richardhawthorn/Wifi7Segment-smd/images/DSC_4980.JPG

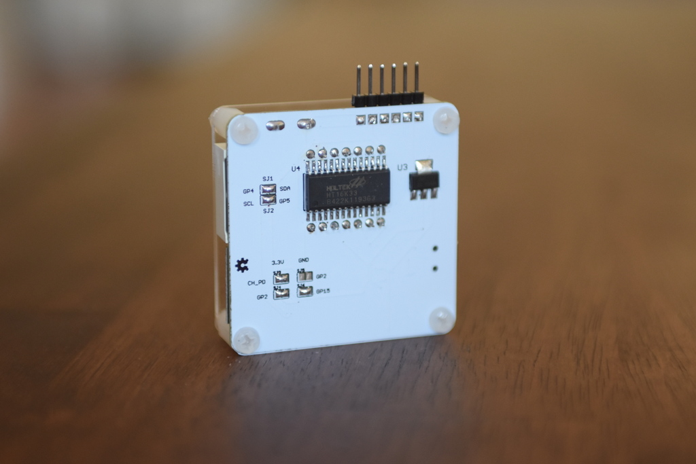
images/DSC_4980.JPG
