richardhawthorn/Wifi7Segment-smd/images/DSC_4983.JPG

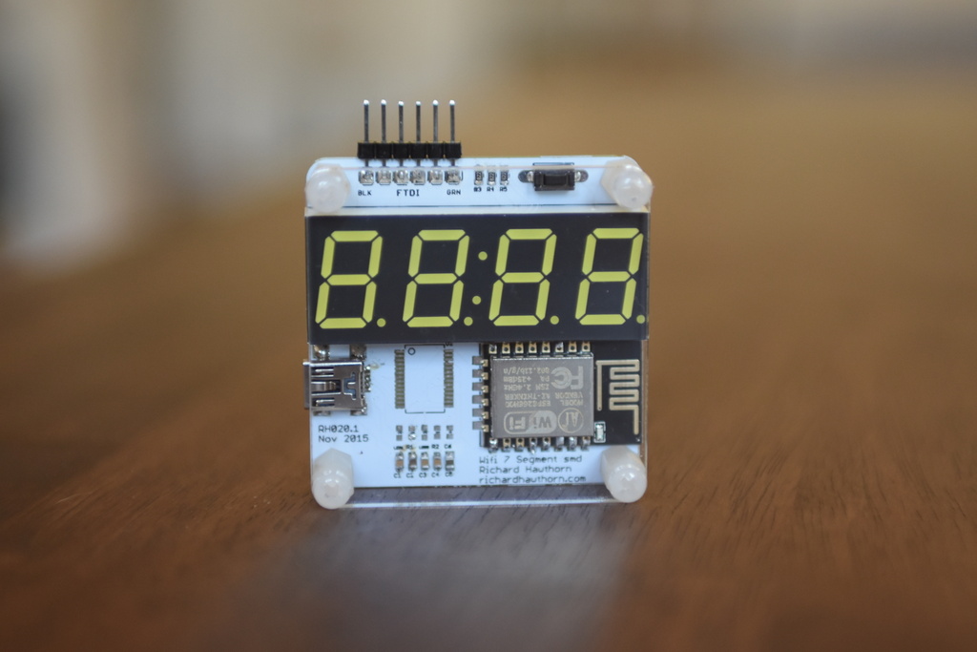
images/DSC_4983.JPG
